Biological-Microsystems-Laboratory/3d-printed-oxygen-control-insert/data/6well.png

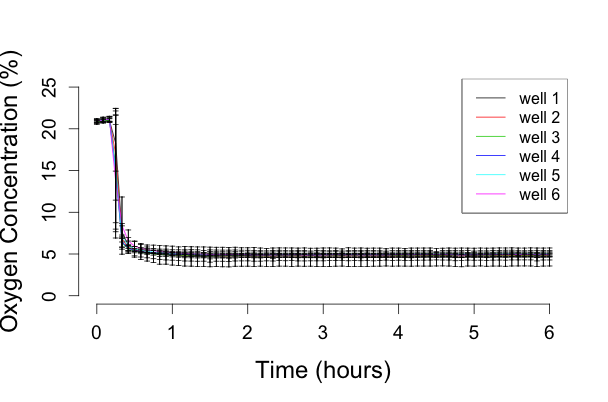
data/6well.png
