Biological-Microsystems-Laboratory/3d-printed-oxygen-control-insert/data/24well.png

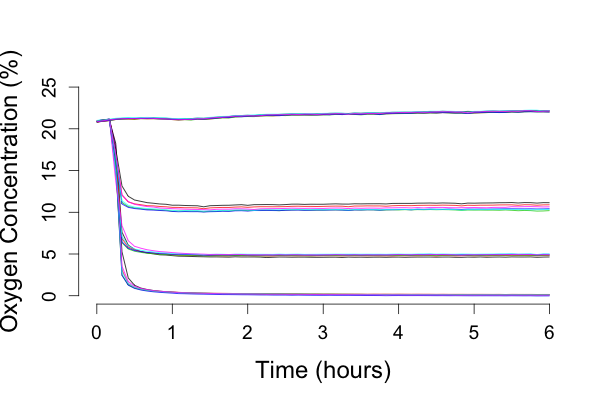
data/24well.png
